whitakerz/Battery-ESP32/Pictures/IMG_1238.jpg

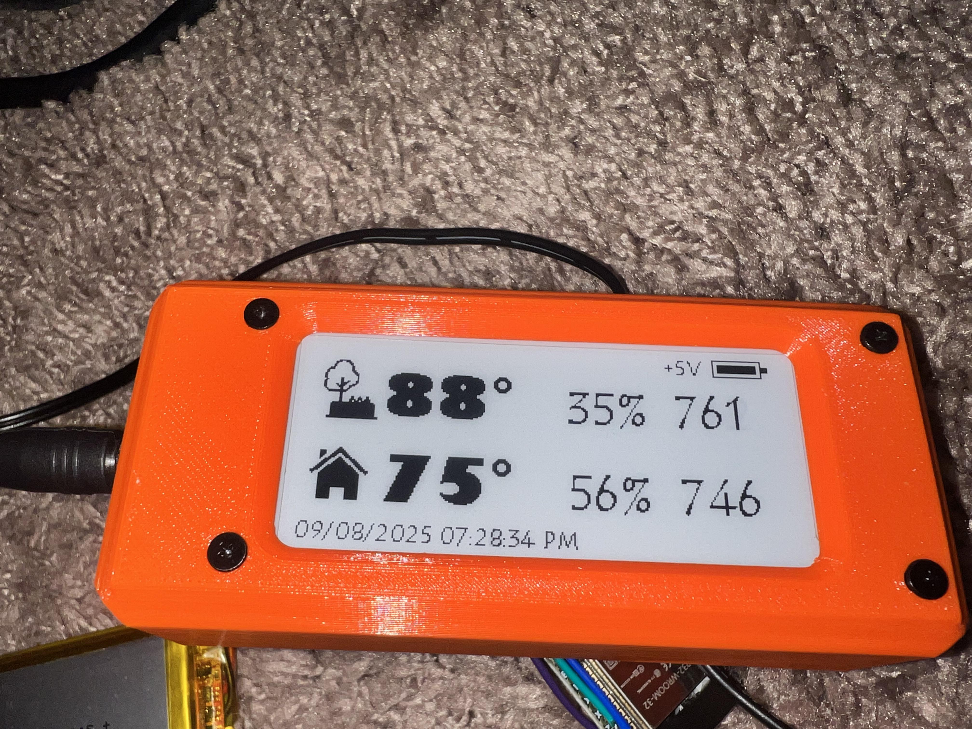
Pictures/IMG_1238.jpg
