whitakerz/Battery-ESP32/Pictures/IMG_1242.jpg

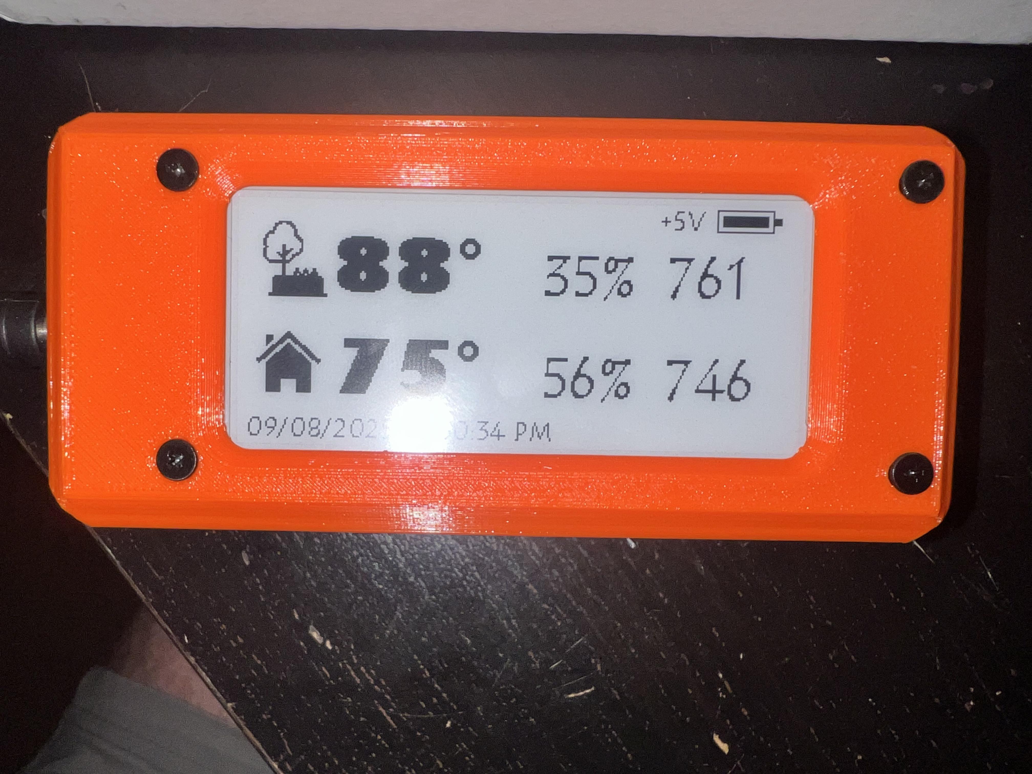
Pictures/IMG_1242.jpg
