whitakerz/Battery-ESP32/Pictures/E ink display case.png

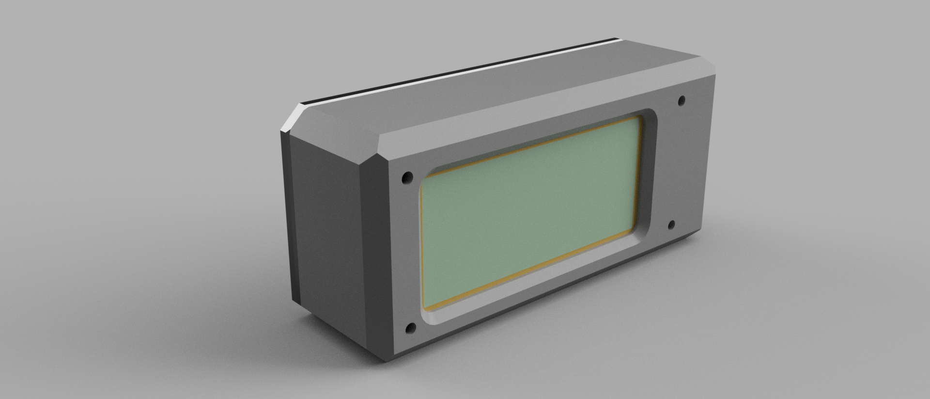
Pictures/E ink display case.png
