whitakerz/Battery-ESP32/Pictures/IMG_1234.jpg

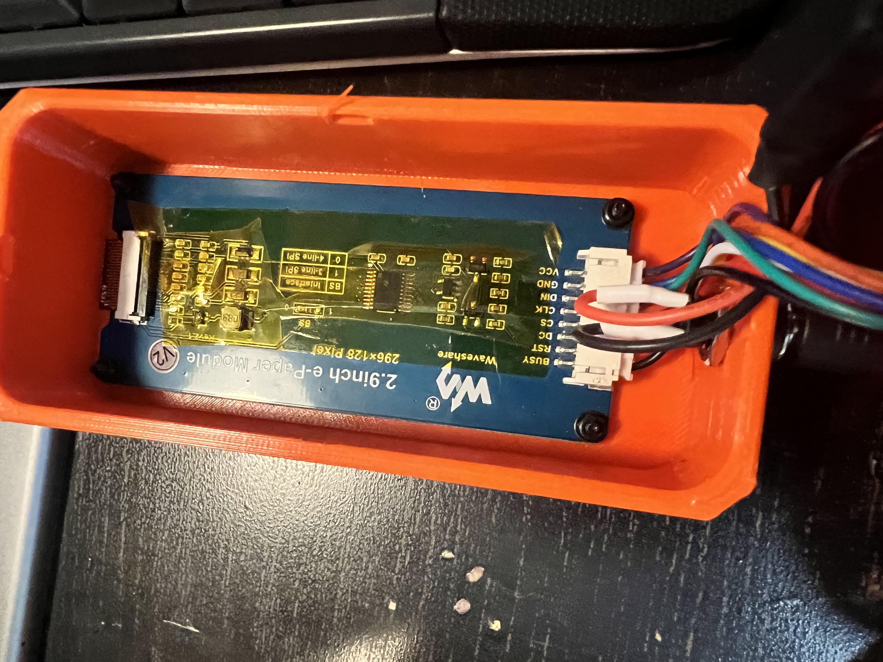
Pictures/IMG_1234.jpg
