whitakerz/Battery-ESP32/Pictures/IMG_1235.jpg

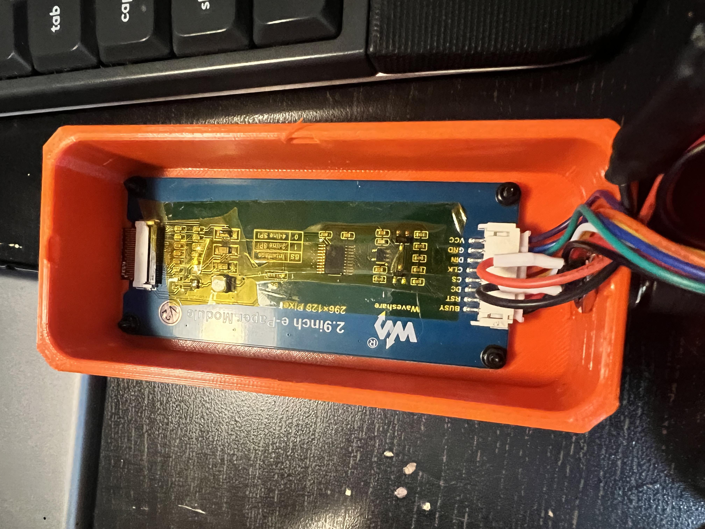
Pictures/IMG_1235.jpg
