whitakerz/Battery-ESP32/Pictures/IMG_1236.jpg

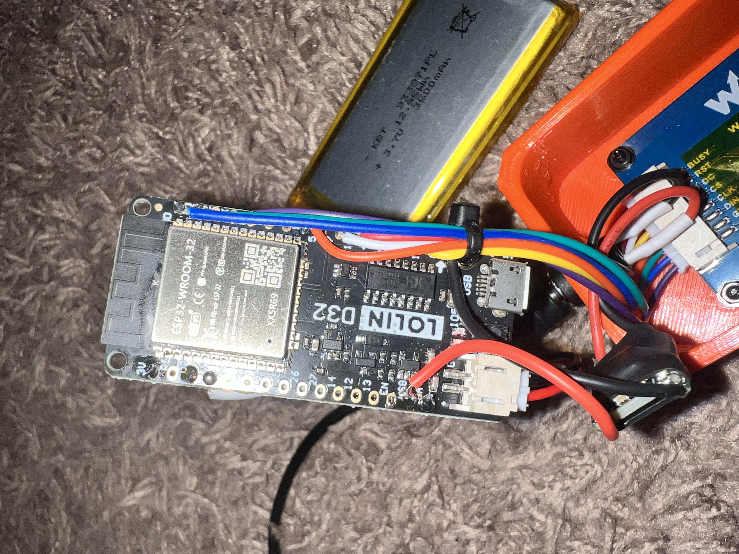
Pictures/IMG_1236.jpg
