whitakerz/Battery-ESP32/Pictures/IMG_1237.jpg

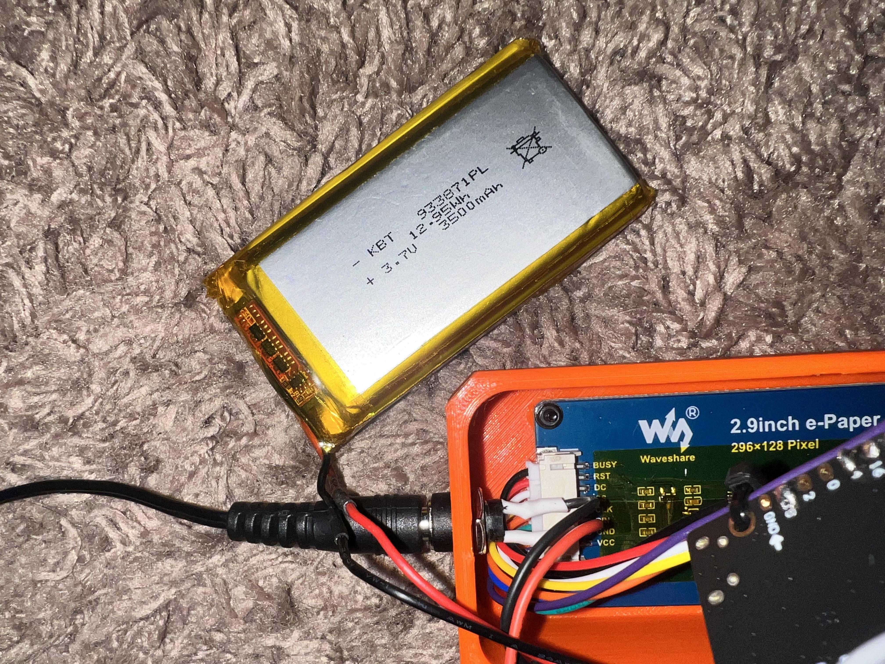
Pictures/IMG_1237.jpg
