whitakerz/Battery-ESP32/Pictures/IMG_1239.jpg

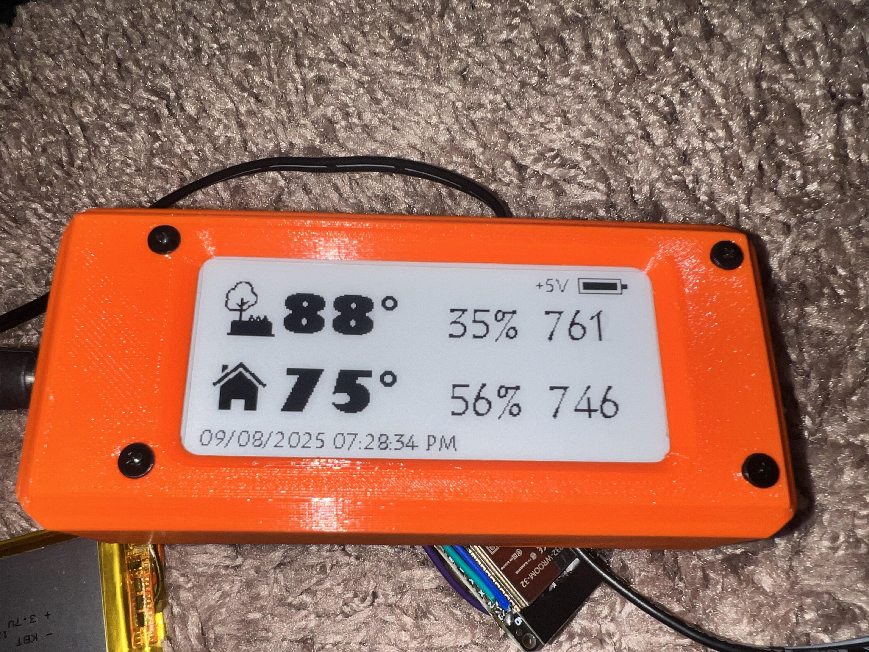
Pictures/IMG_1239.jpg
