whitakerz/Battery-ESP32/Pictures/IMG_1240.jpg

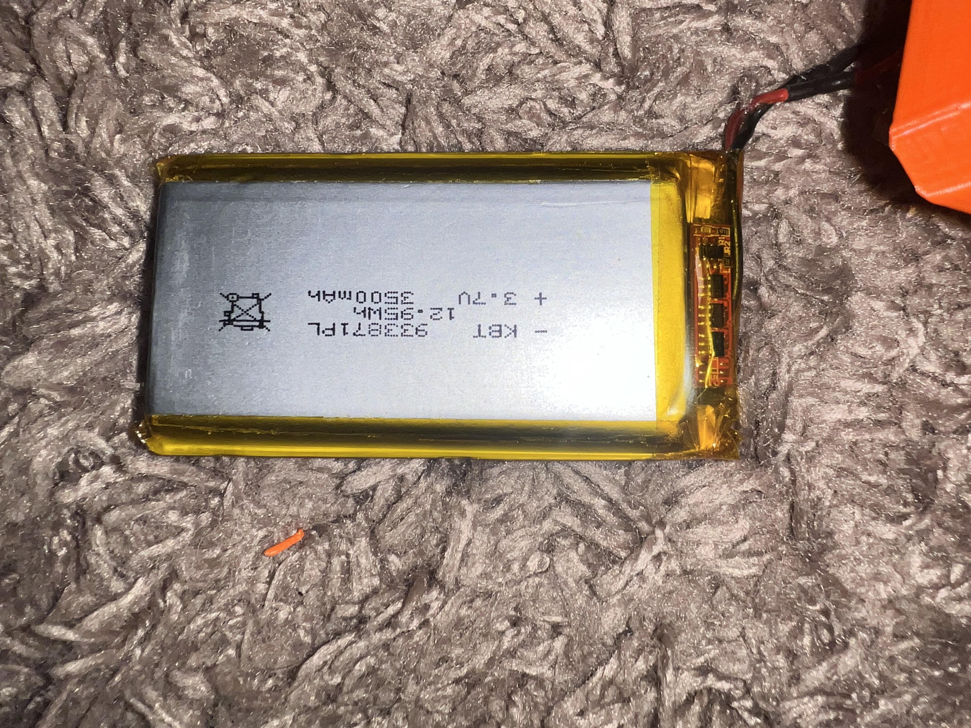
Pictures/IMG_1240.jpg
