whitakerz/Battery-ESP32/Pictures/IMG_1241.jpg

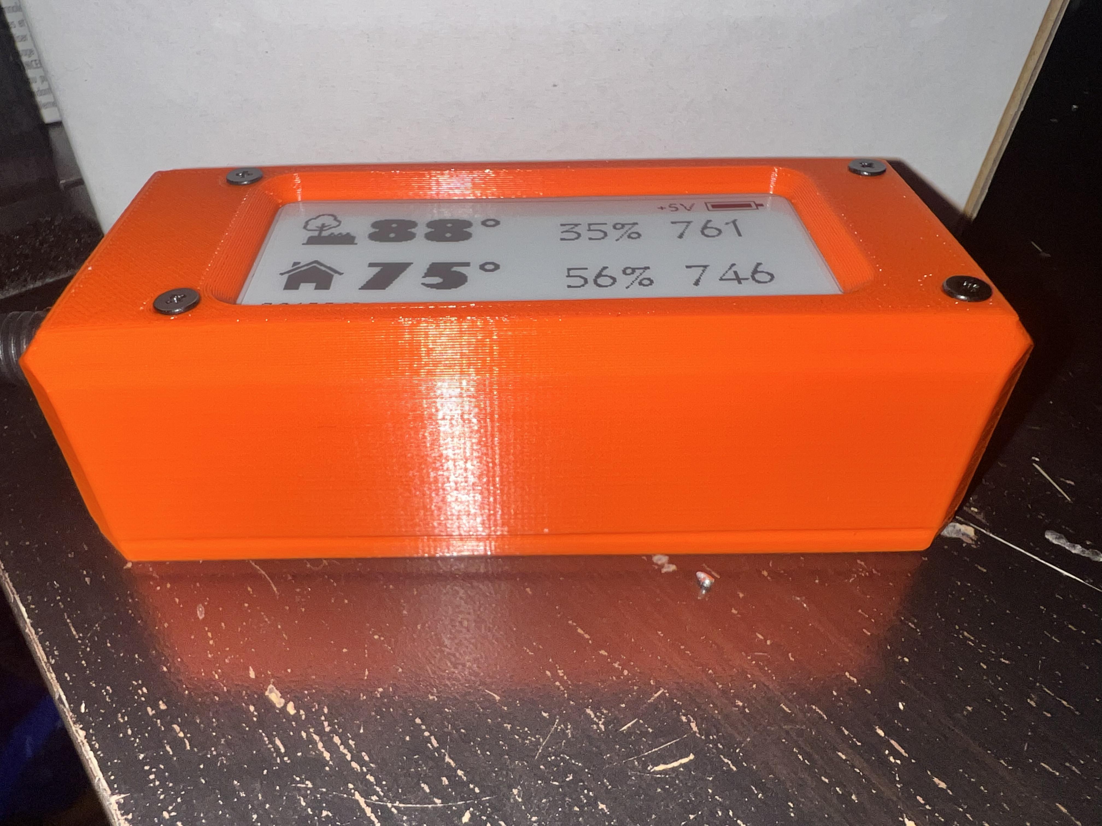
Pictures/IMG_1241.jpg
